l4m4re/SoakageTester/include/Types.h

#ifndef TYPES_H
#define TYPES_H

typedef signed char int8;      //!< 8 bit signed integer data type.
typedef short int16;           //!< 16 bit signed integer data type.
typedef int int32;             //!< 32 bit signed integer data type.
typedef unsigned char uint8;   //!< 8 bit unsigned integer data type.
typedef unsigned short uint16; //!< 16 bit unsigned integer data type.
typedef unsigned int uint32;   //!< 32 bit unsigned integer data type.
typedef float float_t;         //!< float data type.

#endif
