l4m4re/SoakageTester/src/SoakTest.cpp

// SoakTest.cpp
//-----------------------------------------------------------------------------
// Copyright 2017 Arend Lammertink
//
// This file is part of SoakTest.
//
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
//-----------------------------------------------------------------------------

//#include "unistd.h"
#include "time.h"
#include "stdio.h"

#include<iostream>
#include <csignal>
#include <cstdlib>  // for exit
#include <unistd.h> // for usleep

#include"PWM.h"
#include"GPIO.h"
#include"Sampler.h"

#include"Butterworth.h"

using namespace exploringBB;
using namespace std;

//-----------------------------------------------------------------------------

//#define PWM_OUT P9_21 // pin for PWM output
//#define GPO_OUT P9_23 // pin for GPIO output
#define GPIO_OUT 49 // GPIO output P9_23


#define BEDINI
#ifdef BEDINI
#define PWM_START_FREQ 1250
#define PWM_STOP_FREQ  10000
// P9_14 MUST be loaded as a slot before use
static PWM           charge_pwm("pwm_test_P9_14.13"); 
#else
#define PWM_START_FREQ 5000
#define PWM_STOP_FREQ  11000
// P9_21 MUST be loaded as a slot before use
static PWM           charge_pwm("pwm_test_P9_21.12"); 
#endif


static float         charge_pwm_freq     = PWM_START_FREQ;
//static float         charge_pwm_freq     = 500;
//static unsigned int  charge_pwm_duration = 1600;  // in ns. About the minimum
//static unsigned int  charge_pwm_duration = 1750;  // in ns. 
#ifdef BEDINI
//static unsigned int  charge_pwm_duration = 0.1 * 1e9/PWM_START_FREQ;
static float         charge_pwm_duty_perc = 25.0;
#else
static unsigned int  charge_pwm_duration = 30000;  // in ns. 40 us
#endif

// The switch-off time of the circuitry driving the gate of the MOSFET is in
// the order of 300 usec, which means we could maximally drive the circuit at
// about 2 kHz, which is way to slow. 
//
// The opto-driver appears to switch off pretty fast, but the MPSA42's don't.
// Perhaps a base-discharge resistor over these could improve the situation.

static GPIO          _outGPIO(GPIO_OUT);

static Sampler       sampler;

static uint32        startChrgIdx=0, stopChrgIdx=0,
                     startDischrgIdx=0, stopDischrgIdx=0;

//-----------------------------------------------------------------------------

void startCharge()
{
    if(charge_pwm.isRunning())
        charge_pwm.stop();

    for( int idx=0; idx<2; idx++) 
    {
        charge_pwm.setFrequency(charge_pwm_freq);      // Set the period as a frequency
#ifdef BEDINI
        charge_pwm.setDutyPerc(charge_pwm_duty_perc);
#else
        charge_pwm.setDutyCycle(charge_pwm_duration);
#endif
    }

    startChrgIdx = sampler.lastIdx();
    charge_pwm.run();

}

void stopCharge()
{
    //      if (pruiocharge_pwm_setValue(io, PWM_OUT, freq, 0.0)) { // stop charging
    //                printf("failed stoping @PWM (%s)\n", io->Errr); break;}

    if(charge_pwm.isRunning())
        charge_pwm.setDutyCycle(0);

    stopChrgIdx = sampler.lastIdx();
}

void startDischarge()
{
//    if (pruio_gpio_setValue(sampler.io, GPO_OUT, 1)) { //     stop discharging
//        printf("failed discharging stop (%s)\n", sampler.io->Errr); return;}

    startDischrgIdx = sampler.lastIdx();

//    _outGPIO.setDirection(OUTPUT);
    _outGPIO.setValue(HIGH);
}

void stopDischarge()
{
//   if (pruio_gpio_setValue(sampler.io, GPO_OUT, 0)) { //     stop discharging
//       printf("failed discharging stop (%s)\n", sampler.io->Errr); return;}
    
    _outGPIO.setValue(LOW);

    stopDischrgIdx = sampler.lastIdx();
}


void cleanUp()
{
    stopCharge();
    stopDischarge();
    sampler.cleanUp();
}


void signalHandler( int signum ) {
    cout << "Interrupt signal (" << signum << ") received.\n";

    cleanUp();

    exit(signum);
}

#define NO_FILTER
#ifdef NO_FILTER
# define mGetVoltage(idx) sampler.getVoltage(idx)
# define mGetCurrent(idx) sampler.getCurrent(idx)
#else
# define mGetVoltage(idx) voltage[idx]
# define mGetCurrent(idx) current[idx]
#endif


#ifdef NO_FILTER
void buf2file(const char* fname)
#define mNrSamples sampler.nrSamples()
#else
void buf2file(const char* fname, double* voltage, double* current, uint32 nsamples)
#define mNrSamples nsamples
#endif
{
    FILE * pFile;

    pFile = fopen (fname,"w");

    for( uint32 idx=0; idx<mNrSamples; idx++)
    {
        double volt = mGetVoltage(idx);
        double curr = mGetCurrent(idx);
        fprintf(pFile, "%f, %f\n",volt,curr);
        //fprintf(pFile, "%d, %d\n",sampler.volt(idx),sampler.curr(idx));
    }

    fclose (pFile);
}



int main(int argc, char **argv)
{
    // register signal handlers
    signal(SIGINT, signalHandler);
    signal(SIGABRT, signalHandler);
    signal(SIGTERM, signalHandler);

    if( !sampler.ok() ) { cleanUp(); return 1; }

    charge_pwm.stop();
#ifdef BEDINI
    charge_pwm.setPolarity(PWM::ACTIVE_LOW); 
#else
    charge_pwm.setPolarity(PWM::ACTIVE_HIGH);
#endif
    charge_pwm.setDutyCycle(0);
    charge_pwm.run();

    _outGPIO.setDirection(OUTPUT);


    float fully_charged_voltage = 22.0f;   //!< stop charging 
    //float fully_charged_voltage = 7.5f;   //!< stop charging 
    //float fully_discharged_voltage = 0.2f; //!< stop discharging
    float fully_discharged_voltage = 14.5f; //!< stop discharging

    float v_val = 0.0f;
    float max_perc = 0.0f;

//    if (pruio_gpio_setValue(sampler.io, GPO_OUT, 0)) { //         configure GPIO
//         printf("setValue @GPO_OUT error (%s)\n", sampler.io->Errr); return 1;}
             

    startDischarge();

    usleep( 10000000 ); // 1 sec

    stopDischarge();

    sampler.calibrateCurrent();

    if( !sampler.ok() || !sampler.nrSamples() )
    {
        printf("Sampler error while calibrating (%s)\n", sampler.errMsg());
        sampler.reset();
    }

    printf("Sampler current mean: %5.2f\n", sampler.currentMean() );

    printf("run, freq, injoules, outjoules, perc, sampler_current_mean\n");

    bool error = false;
    uint32 n=1;
    for(;;)
    {
//        float v_max = 0;
//        float v_min = 65000;

//        printf("Start charging.\n");
        sampler.reset();
        usleep( 100 ); // 100 usec
//        sampler.calibrateCurrent();

        startCharge();

        const uint32 n_smp=8;

        bool done=false;
        do { //                               wait for end of charge cycle

            done = true;
            for( uint32 cnt=0; cnt < n_smp; cnt++ )
            {
                v_val = sampler.getVoltage( sampler.lastIdx()-cnt );
/*
                if( v_val > v_max)
                {
                    v_max = v_val;
                    printf("Max voltage: %d\n", v_max);
                }
*/

                if (v_val <= fully_charged_voltage) { done=false; break;}
            }

            if( !sampler.ok() || !sampler.nrSamples() )
            {
                printf("Sampler error while charging (%s)\n", sampler.errMsg());
                done = true;

                sampler.reset();
                error = true;
            }

            //usleep(500); // At 500 us, we will fetch about 100 samples 
            usleep(5000); // At 500 us, we will fetch about 100 samples 

        } while( !done );

//        printf("V_max: %d\n",v_max);

        stopCharge();

        usleep( 1000 ); // 1 msec
//        usleep( 50000 ); // 50 msec
//        sampler.calibrateCurrent();

//        printf("Start discharging.\n");

        startDischarge();

#define USEAVEAGE
#ifdef USEAVEAGE
        done=false;
        do { //                               wait for end of discharge cycle
            done = true;

            for( uint32 cnt=0; cnt < n_smp; cnt++ )
            {
                v_val = sampler.getVoltage( sampler.lastIdx()-cnt );
/*
                if( v_val < v_min)
                {
                    v_min = v_val;
                    printf("Min voltage: %d\n", v_min);
                }
*/

                if (v_val >= fully_discharged_voltage) { done=false; break;}
            }

            if( !sampler.ok() )
            {
                printf("Sampler error while discharging (%s)\n", sampler.errMsg());
                sampler.reset();
                error = true;
                done = true;
                usleep( 500000 );// make sure we've discharged
            }

            usleep(10); // At 500 us, we will fetch about 100 samples 
        } while( !done );
#else
        while( sampler.getVoltage( sampler.lastIdx() ) > fully_discharged_voltage)
        {
            usleep(10);
        }
#endif

//        usleep( 10000 ); // 10 msec
//        usleep( 1000 ); // 1 msec

        stopDischarge();

        usleep( 1000 ); // 1 msec
//        usleep( 10000 ); // 10 msec

//        printf("Calibrate current.\n");
//        sampler.calibrateCurrent();
        sampler.stop();

        if( !error && sampler.ok() ) 
        {
        // Compute in/out Joules from buffer
            double inJoules = 0, outJoules = 0;
    //        int stage=0;


#ifndef NO_FILTER
            uint32 nsamples = sampler.nrSamples();
            double* voltage = new double[nsamples];
            double* current = new double[nsamples];

            for( uint32 idx=0; idx<nsamples; idx++)
            {
                voltage[idx] = sampler.getVoltage(idx);
                current[idx] = sampler.getCurrent(idx);
            }

            Butterworth volt_lpFilter;
            Butterworth curr_lpFilter;

            // filter a buffer of input samples, in-place
            for (uint32 idx = 0; idx < nsamples; idx++) 
            {
                voltage[idx] = volt_lpFilter.process(voltage[idx]);
                current[idx] = curr_lpFilter.process(current[idx]);
            }
#endif

    //define PRINT_OUTPUT

#ifdef PRINT_OUTPUT        
            printf("-- start  --\n");
            for( uint32 idx=0; idx<startChrgIdx; idx++)
            {
                double volt = mGetVoltage(idx);
                double curr = mGetCurrent(idx);
                printf("%f, %f, %d\n",volt,curr,stage);
            }

            stage++;
            printf("-- charge --\n");
#endif
            for( uint32 idx=startChrgIdx; idx<stopChrgIdx; idx++)
            {
                double volt = mGetVoltage(idx);
                double curr = mGetCurrent(idx);
#ifdef PRINT_OUTPUT        
                printf("%f, %f, %d\n",volt,curr,stage);
#endif

    //            double dPow = curr * volt * sampler.period();
                double dPow = curr * volt / SampleRate;
                inJoules += dPow;
            }

#ifdef PRINT_OUTPUT        
            stage++;
            printf("-- pause --\n");
            for( uint32 idx=stopChrgIdx; idx<startDischrgIdx; idx++)
            {
                double volt = mGetVoltage(idx);
                double curr = mGetCurrent(idx);
                printf("%f, %f, %d\n",volt,curr,stage);
            }

            stage++;
            printf("-- discharge --\n");
#endif
            for( uint32 idx=startDischrgIdx; idx<stopDischrgIdx; idx++)
            {
                double volt = mGetVoltage(idx);
                double curr = mGetCurrent(idx);
#ifdef PRINT_OUTPUT        
                printf("%f, %f, %d\n",volt,curr,stage);
#endif

    //            double dPow = curr * volt * sampler.period();
                double dPow = curr * volt / SampleRate;
                outJoules += dPow;
            }
            outJoules *= -1.0f;

#ifdef PRINT_OUTPUT        
            stage++;
            printf("-- lead out --\n");
            for( uint32 idx=stopDischrgIdx; idx<sampler.nrSamples(); idx++)
            {
                double volt = mGetVoltage(idx);
                double curr = mGetCurrent(idx);
                printf("%f, %f, %d\n",volt,curr,stage);
            }
#endif

    /*
            usleep( 10000 );

            printf("-- done --\n");

            printf("Indexes: %d, %d, %d, %d, %d \n", startChrgIdx, stopChrgIdx, startDischrgIdx, stopDischrgIdx, sampler.nrSamples());
            printf("Joules in  : %f\n",inJoules);
            printf("Joules out : %f\n",outJoules);
            printf("Perc out/in: %f\n",100.0f*outJoules/inJoules);
    */


            float perc = 100.0f*outJoules/inJoules;

#ifdef BEDINI
            printf("%d, %5.2f, %3.2f, %5.4f, %5.4f, %3.4f, %5.4f\n",
                    n, charge_pwm_freq, charge_pwm_duty_perc,
#else
            printf("%d, %5.2f, %d, %5.4f, %5.4f, %3.4f, %5.4f\n",
                    n, charge_pwm_freq, charge_pwm_duration,
#endif
                    inJoules, outJoules, perc,
                    sampler.currentMean());
#ifdef BEDINI
            if( perc > max_perc && n>10 && perc > 50.0 )
#else
            if( perc > max_perc && n>10 
               || perc > 100.0 )
#endif
            {
                max_perc = perc;

#define     PATH "/data/arend/work/SoakageTester/bin"

                char filename[256];
                sprintf( filename, "%s/%.2f-%.2f-%2.0f.log",
                         PATH,perc,charge_pwm_freq,charge_pwm_duty_perc
                       );

                printf("Saving best result to: %s \n",filename);

#ifdef NO_FILTER
                buf2file( filename );
#else
                buf2file( filename,
                          voltage, current, nsamples);
#endif
            }

            charge_pwm_freq *= 1.01; 
            //charge_pwm_freq += 11;
            //
#ifndef NO_FILTER
        delete[] voltage;
        delete[] current;
#endif

            
        }
        

#ifdef BEDINI
        if( charge_pwm_freq  > PWM_STOP_FREQ || error  )
        { 
            error = false;
            charge_pwm_freq = PWM_START_FREQ;
            charge_pwm_duty_perc += 1;
        }
#else
        float duty = charge_pwm_duration/(1e9/charge_pwm_freq);
        if( charge_pwm_freq  > PWM_STOP_FREQ || duty > 0.9 )
        { 
            charge_pwm_freq = PWM_START_FREQ;
            charge_pwm_duration += 1000;
        }
#endif

        if( ! sampler.ok() )
        { 
            printf("Sampler error after computation (%s)\n", sampler.errMsg());
            sampler.reset();
        }

        if( !sampler.ok() )
        { 
            printf("Still Sampler error after reset. (%s)\n", sampler.errMsg());
            cleanUp(); 
            return 1;
        }

        if( charge_pwm_duty_perc > 95.0 )
        { 
            printf("Finished run.");
            cleanUp(); 
            return 0;
        }

//        sampler.calibrateCurrent();

        n++;
    }

    cleanUp();

//    printDebugInfo();
    return 0;
}
